chris-heo/usb-share/hardware/usbshare_0.2.sch

## EAGLE design hardware/usbshare_0.2.sch (2022-02-27)

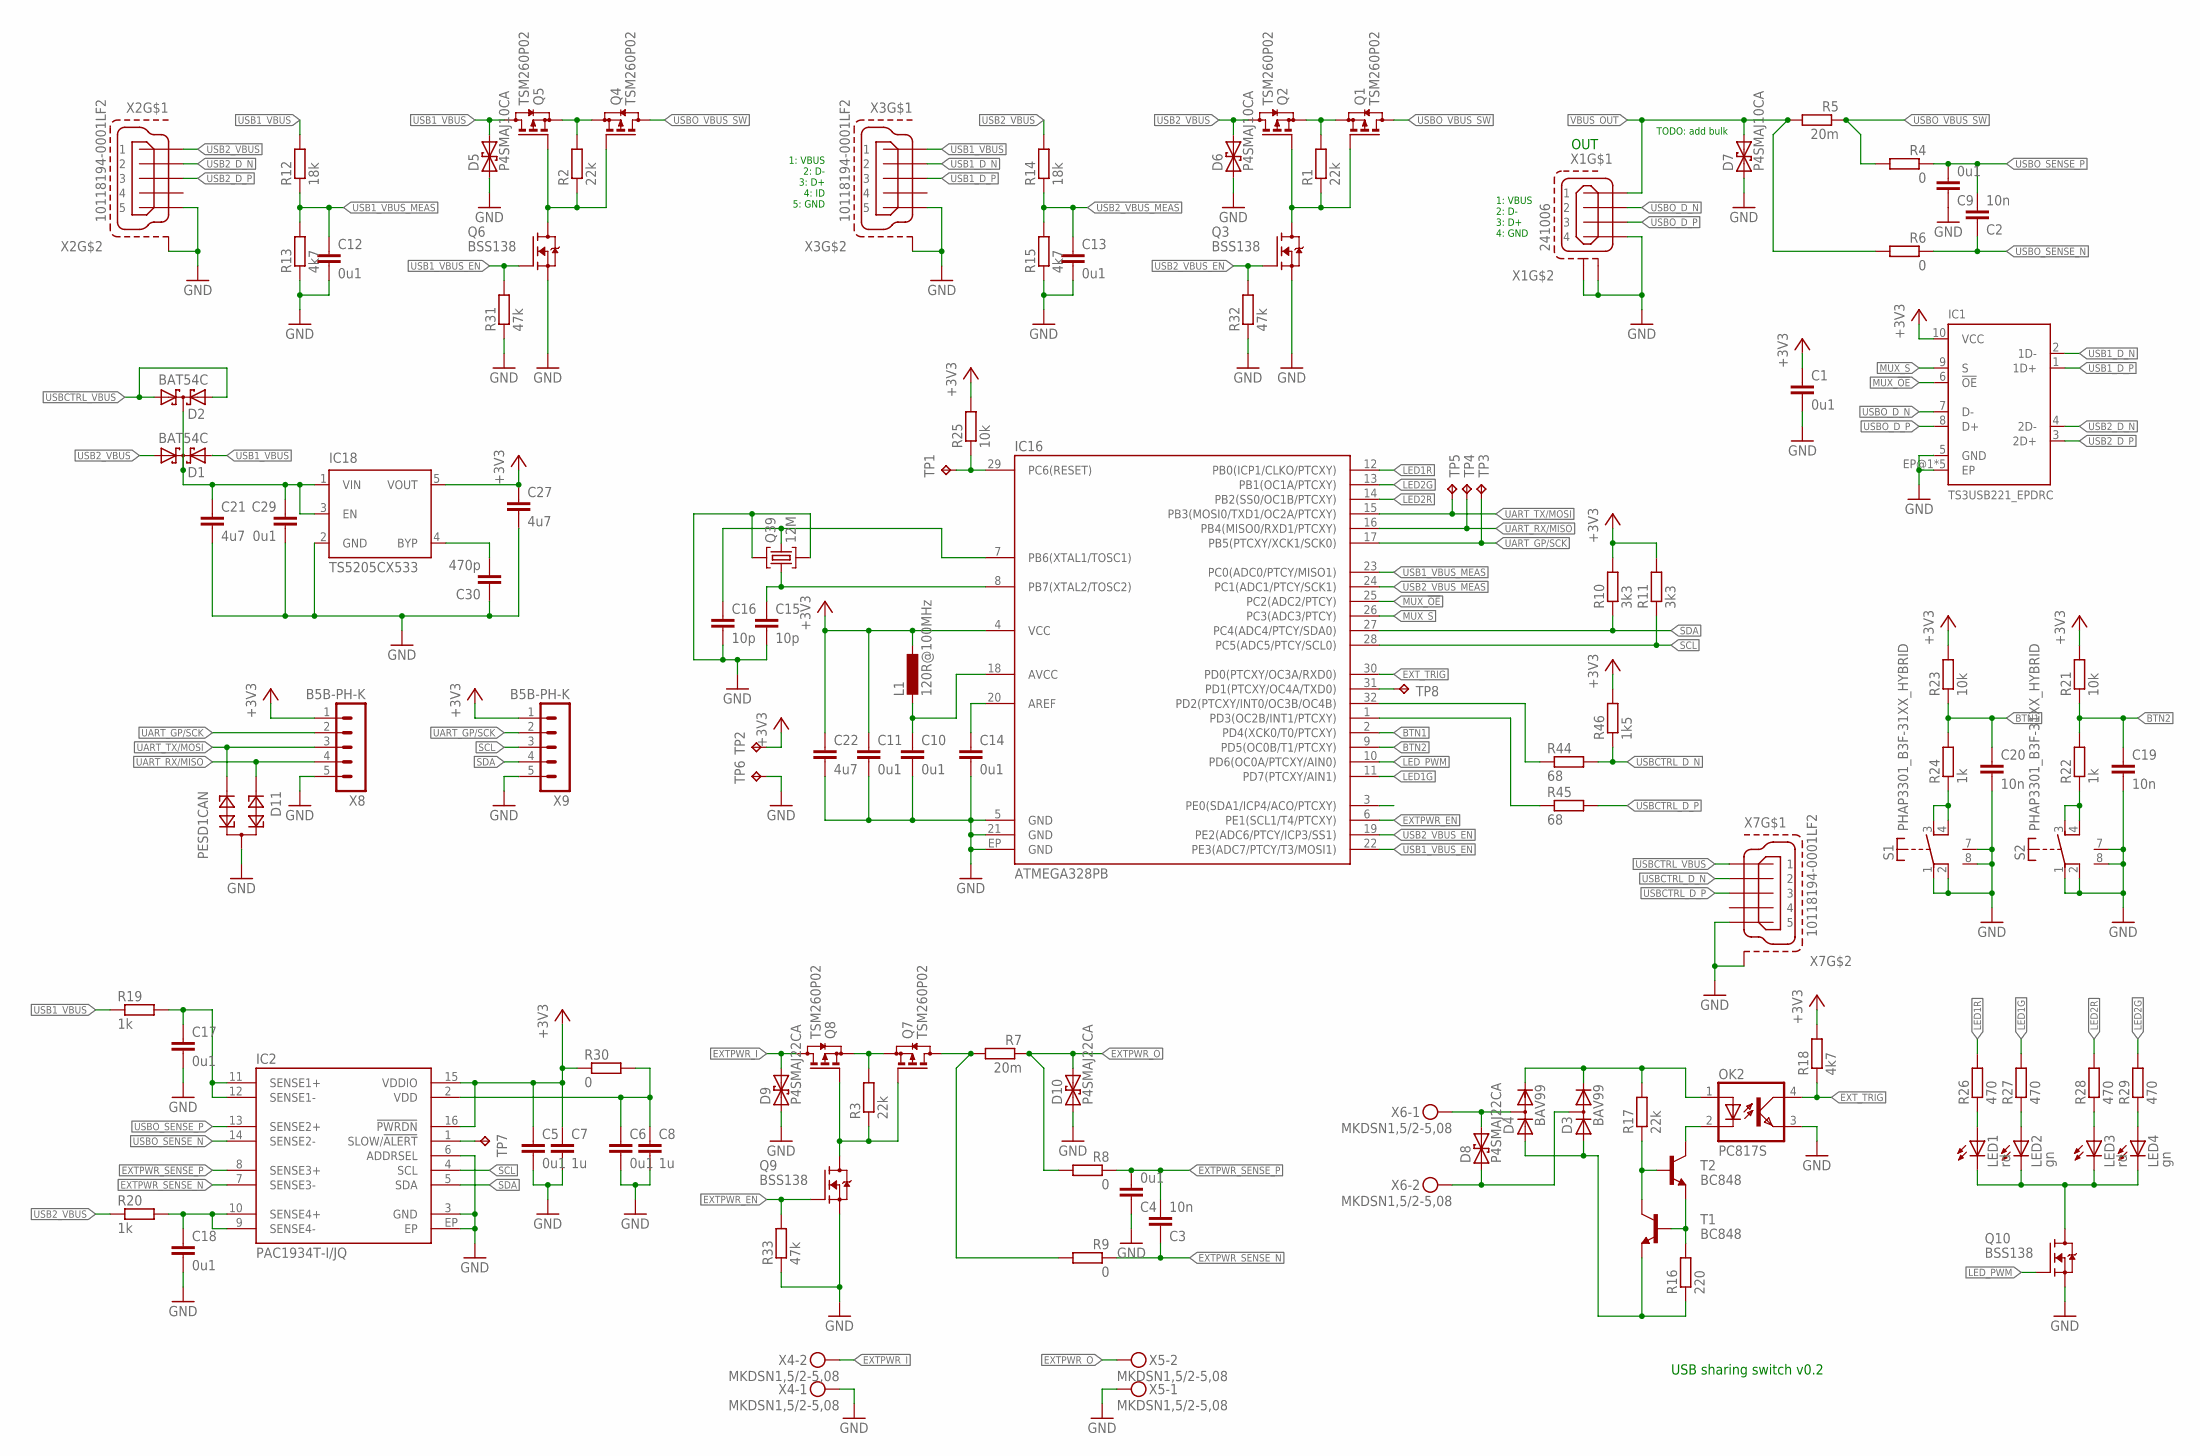
[picture p6: schematic usbshare_0.2.sch]

Parts:
C1, C5, C6, C10, C11, C14: 0u1; C0402
C2, C3, C19, C20: 10n; C0603
C4, C9, C12, C13, C17, C18, C29: 0u1; C0603
C7, C8: 1u; C0603
C15, C16: 10p; C0603
C21: 4u7; C0805
C22, C27: 4u7; C0603
C30: 470p; C0603
D1, D2: BAT54C; SOT23
D3, D4: BAV99; SOT23
D5, D6, D7: P4SMAJ10CA; DO214AC
D8, D9, D10: P4SMAJ22CA; DO214AC
D11: PESD1CAN; SOT23
IC1: TS3USB221_EPDRC; S-PVSON-N10
IC2: PAC1934T-I/JQ; UQFN16
IC16: ATMEGA328PB; VQFN32
IC18: TS5205CX533; SOT23-5
L1: 120R@100MHz; L2012C
LED1, LED3: rd; CHIP-LED0603
LED2, LED4: gn; CHIP-LED0603
OK2: PC817S; SMD4-9
Q1, Q2, Q4, Q5, Q7, Q8: TSM260P02; SOT23
Q3, Q6, Q9, Q10: BSS138; SOT23
Q39: 12M; MJ
R1, R2, R3, R17: 22k; R0603
R4, R6, R8, R9, R30: 0; R0603
R5, R7: 20m; R0603
R10, R11: 3k3; R0603
R12, R14: 18k; R0603
R13, R15, R18: 4k7; R0603
R16: 220; R0603
R19, R20, R22, R24: 1k; R0603
R21, R23, R25: 10k; R0603
R26, R27, R28, R29: 470; R0603
R31, R32, R33: 47k; R0402
R44, R45: 68; R0603
R46: 1k5; R0402
S1, S2: PHAP3301_B3F-31XX_HYBRID
T1, T2: BC848; SOT23
TP1, TP2, TP3, TP4, TP5, TP6, TP7, TP8: TPTP13R; TP13R
X1: 241006
X2, X3, X7: 10118194-0001LF2; 10118194-0001LF_2
X4, X5, X6: MKDSN1,5/2-5,08
X8, X9: B5B-PH-K

Connections:
+3V3: C1.1, C5.1, C7.1, C11.1, C22.1, C27.1, IC1.10 (VCC), IC2.15 (VDDIO), IC2.16 (!PWRDN), IC16.4 (VCC), IC18.5 (VOUT), L1.1, R10.2, R11.2, R18.2, R21.2, R23.2, R25.2, R30.1, R46.2, TP2.TP, X8.1, X9.1
AGND: D3.1 (A), D4.1 (A), R16.1, T1.2 (E)
BTN1: C20.1, IC16.2 (PD4(XCK0/T0/PTCXY)), R23.1, R24.2
BTN2: C19.1, IC16.9 (PD5(OC0B/T1/PTCXY)), R21.1, R22.2
EXTPWR_EN: IC16.6 (PE1(SCL1/T4/PTCXY)), Q9.1 (G), R33.2
EXTPWR_I: D9.2, Q8.3 (D), X4.2
EXTPWR_MID: Q7.3 (D), R7.2, R9.2
EXTPWR_O: D10.2, R7.1, R8.2, X5.2
EXTPWR_SENSE_N: C3.1, IC2.7 (SENSE3-), R9.1
EXTPWR_SENSE_P: C3.2, C4.2, IC2.8 (SENSE3+), R8.1
EXT_TRIG: IC16.30 (PD0(PTCXY/OC3A/RXD0)), OK2.4 (COL), R18.1
GND: C1.2, C4.1, C5.2, C6.2, C7.2, C8.2, C9.1, C10.2, C11.2, C12.2, C13.2, C14.2, C15.2, C16.2, C17.2, C18.2, C19.2, C20.2, C21.2, C22.2, C27.2, C29.2, C30.1, D5.1, D6.1, D7.1, D9.1, D10.1, D11.3, IC1.5 (GND), IC1.EP@1 (EP), IC2.3 (GND), IC2.6 (ADDRSEL), IC2.EP, IC16.5 (GND), IC16.21 (GND), IC16.EP (GND), IC18.2 (GND), OK2.3 (EMIT), Q3.2 (S), Q6.2 (S), Q9.2 (S), Q10.2 (S), Q39.2, Q39.4, R13.1, R15.1, R31.1, R32.1, R33.1, S1.1, S1.2 (P1), S1.7 (M1), S1.8 (M2), S2.1, S2.2 (P1), S2.7 (M1), S2.8 (M2), TP6.TP, X1.4, X1.5 (S1), X1.6 (S2), X2.5, X2.S1, X3.5, X3.S1, X4.1, X5.1, X7.5, X7.S1, X8.5, X9.5
LED1G: IC16.11 (PD7(PTCXY/AIN1)), R27.2
LED1R: IC16.12 (PB0(ICP1/CLKO/PTCXY)), R26.2
LED2G: IC16.13 (PB1(OC1A/PTCXY)), R29.2
LED2R: IC16.14 (PB2(SS0/OC1B/PTCXY)), R28.2
LED_PWM: IC16.10 (PD6(OC0A/PTCXY/AIN0)), Q10.1 (G)
MUX_!OE!: IC1.6 (!OE), IC16.25 (PC2(ADC2/PTCY))
MUX_S: IC1.9 (S), IC16.26 (PC3(ADC3/PTCY))
unnamed: Q1.1 (G), Q2.1 (G), Q3.3 (D), R1.1
unnamed: C21.1, C29.1, D1.3 (CC), D2.3 (CC), IC18.1 (VIN), IC18.3 (EN)
unnamed: Q4.2 (S), Q5.2 (S), R2.2
unnamed: Q1.2 (S), Q2.2 (S), R1.2
unnamed: Q4.1 (G), Q5.1 (G), Q6.3 (D), R2.1
unnamed: Q7.2 (S), Q8.2 (S), R3.2
unnamed: Q7.1 (G), Q8.1 (G), Q9.3 (D), R3.1
unnamed: C14.1, IC16.20 (AREF)
unnamed: R16.2, T1.1 (B), T2.2 (E)
unnamed: LED1.C, LED2.C, LED3.C, LED4.C, Q10.3 (D)
unnamed: OK2.2 (C), T2.3 (C)
unnamed: R17.1, T1.3 (C), T2.1 (B)
unnamed: D3.2 (C), D4.2 (C), OK2.1 (A), R17.2
unnamed: D4.3 (AC), D8.2, X6.1
unnamed: D3.3 (AC), D8.1, X6.2
unnamed: C10.1, IC16.18 (AVCC), L1.2
unnamed: C17.1, IC2.11 (SENSE1+), IC2.12 (SENSE1-), R19.2
unnamed: C18.1, IC2.9 (SENSE4-), IC2.10 (SENSE4+), R20.2
unnamed: LED1.A, R26.1
unnamed: LED2.A, R27.1
unnamed: R22.1, S2.3 (S), S2.4 (S1)
unnamed: C6.1, C8.1, IC2.2 (VDD), R30.2
unnamed: IC16.29 (PC6(RESET)), R25.1, TP1.TP
unnamed: LED3.A, R28.1
unnamed: R24.1, S1.3 (S), S1.4 (S1)
unnamed: LED4.A, R29.1
unnamed: IC2.1 (SLOW/!ALERT), TP7.TP
unnamed: IC16.31 (PD1(PTCXY/OC4A/TXD0)), TP8.TP
unnamed: C15.1, IC16.8 (PB7(XTAL2/TOSC2)), Q39.1
unnamed: C16.1, IC16.7 (PB6(XTAL1/TOSC1)), Q39.3
unnamed: C30.2, IC18.4 (BYP)
SCL: IC2.4 (SCL), IC16.28 (PC5(ADC5/PTCY/SCL0)), R11.1, X9.3
SDA: IC2.5 (SDA), IC16.27 (PC4(ADC4/PTCY/SDA0)), R10.1, X9.4
UART_GP/SCK: IC16.17 (PB5(PTCXY/XCK1/SCK0)), TP3.TP, X8.2, X9.2
UART_RX/MISO: D11.1, IC16.16 (PB4(MISO0/RXD1/PTCXY)), TP4.TP, X8.4
UART_TX/MOSI: D11.2, IC16.15 (PB3(MOSI0/TXD1/OC2A/PTCXY)), TP5.TP, X8.3
USB1_D_N: IC1.2 (1D-), X3.2
USB1_D_P: IC1.1 (1D+), X3.3
USB1_VBUS: D1.2 (A2), D5.2, Q5.3 (D), R12.2, R19.1, X3.1
USB1_VBUS_EN: IC16.22 (PE3(ADC7/PTCY/T3/MOSI1)), Q6.1 (G), R31.2
USB1_VBUS_MEAS: C12.1, IC16.23 (PC0(ADC0/PTCY/MISO1)), R12.1, R13.2
USB2_D_N: IC1.4 (2D-), X2.2
USB2_D_P: IC1.3 (2D+), X2.3
USB2_VBUS: D1.1 (A1), D6.2, Q2.3 (D), R14.2, R20.1, X2.1
USB2_VBUS_EN: IC16.19 (PE2(ADC6/PTCY/ICP3/SS1)), Q3.1 (G), R32.2
USB2_VBUS_MEAS: C13.1, IC16.24 (PC1(ADC1/PTCY/SCK1)), R14.1, R15.2
USBCTRL_D1_N: IC16.32 (PD2(PTCXY/INT0/OC3B/OC4B)), R44.1
USBCTRL_D1_P: IC16.1 (PD3(OC2B/INT1/PTCXY)), R45.1
USBCTRL_D_N: R44.2, R46.1, X7.2
USBCTRL_D_P: R45.2, X7.3
USBCTRL_VBUS: D2.1 (A1), D2.2 (A2), X7.1
USBO_D_N: IC1.7 (D-), X1.2
USBO_D_P: IC1.8 (D+), X1.3
USBO_SENSE_N: C2.1, IC2.14 (SENSE2-), R6.1
USBO_SENSE_P: C2.2, C9.2, IC2.13 (SENSE2+), R4.1
USBO_VBUS_SW: Q1.3 (D), Q4.3 (D), R4.2, R5.1
VBUS_OUT: D7.2, R5.2, R6.2, X1.1

Notes on the sheet:
OUT
1: VBUS 2: D- 3: D+ 4: GND
1: VBUS 2: D- 3: D+ 4: ID 5: GND
TODO: add bulk
USB sharing switch v0.2
