chris-heo/usb-share/bootloader/usb-share_bolo/usbhiddescriptor.h

/*
 * usbhiddescriptor.h
 *
 * Created: 22.02.2022 21:46:43
 *  Author: Chris
 */ 


#ifndef USBHIDDESCRIPTOR_H_
#define USBHIDDESCRIPTOR_H_

const PROGMEM char usbHidReportDescriptor[33] = 
{
    0x06, 0x00, 0xff,              // USAGE_PAGE (Generic Desktop)
    0x09, 0x01,                    // USAGE (Vendor Usage 1)
    0xa1, 0x01,                    // COLLECTION (Application)
    0x15, 0x00,                    //   LOGICAL_MINIMUM (0)
    0x26, 0xff, 0x00,              //   LOGICAL_MAXIMUM (255)
    0x75, 0x08,                    //   REPORT_SIZE (8)

    0x85, 0x01,                    //   REPORT_ID (1)
    0x95, 0x06,                    //   REPORT_COUNT (6)
    0x09, 0x00,                    //   USAGE (Undefined)
    0xb2, 0x02, 0x01,              //   FEATURE (Data,Var,Abs,Buf)

    0x85, 0x02,                    //   REPORT_ID (2)
    0x95, 0x83,                    //   REPORT_COUNT (131)
    0x09, 0x00,                    //   USAGE (Undefined)
    0xb2, 0x02, 0x01,              //   FEATURE (Data,Var,Abs,Buf)
    0xc0                           // END_COLLECTION
};



#endif /* USBHIDDESCRIPTOR_H_ */
